LeeGillie/lumos-ultra-exhaust-monitor/cad/out/render_side.png

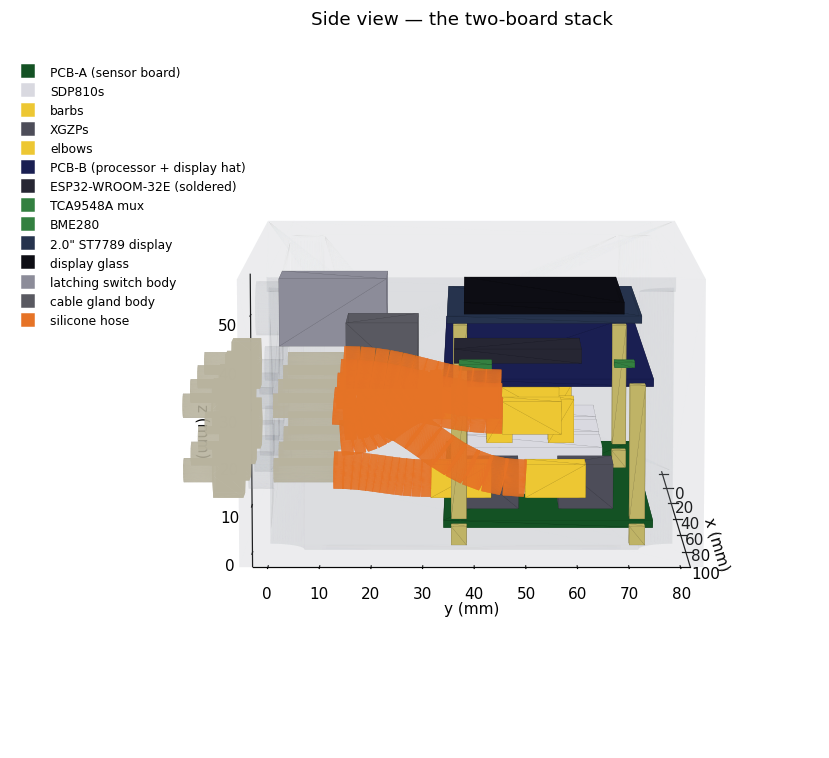
cad/out/render_side.png
