LeeGillie/lumos-ultra-exhaust-monitor/cad/out/render_top.png

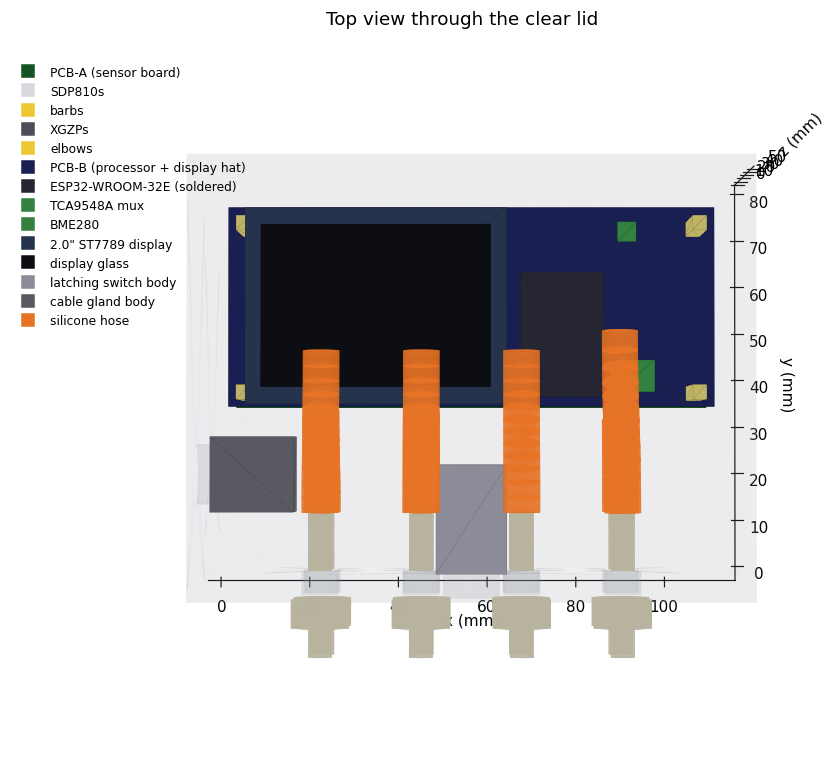
cad/out/render_top.png
