LeeGillie/lumos-ultra-exhaust-monitor/docs/3D Models/Project/renders/sensor_bay_v1.png

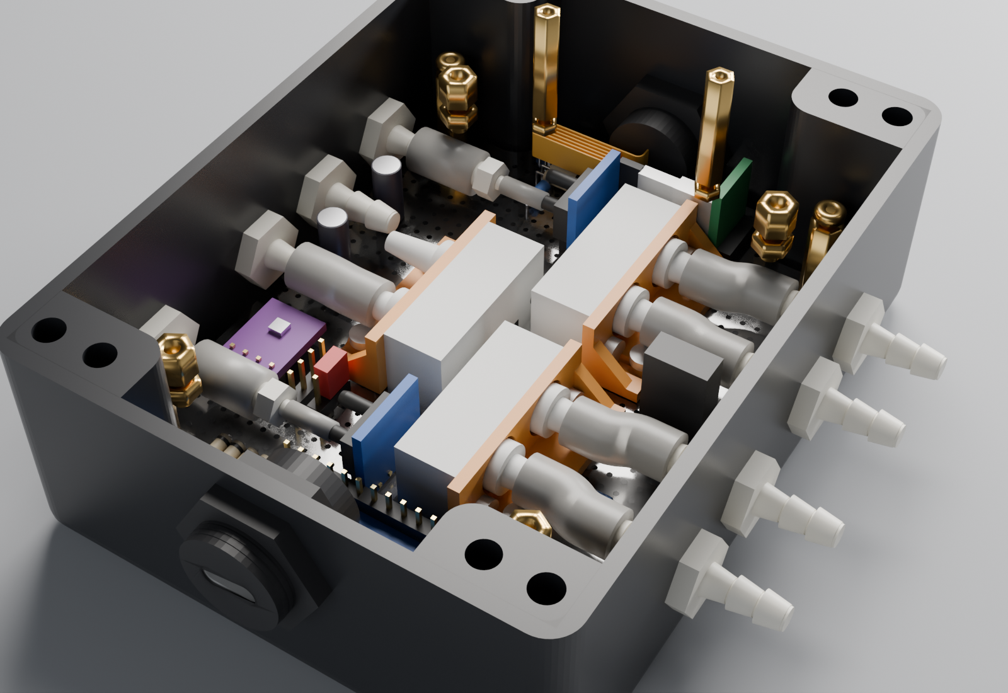
docs/3D Models/Project/renders/sensor_bay_v1.png
