LeeGillie/lumos-ultra-exhaust-monitor/docs/3D Models/Project/textures/mark_fan_node_ANT.png

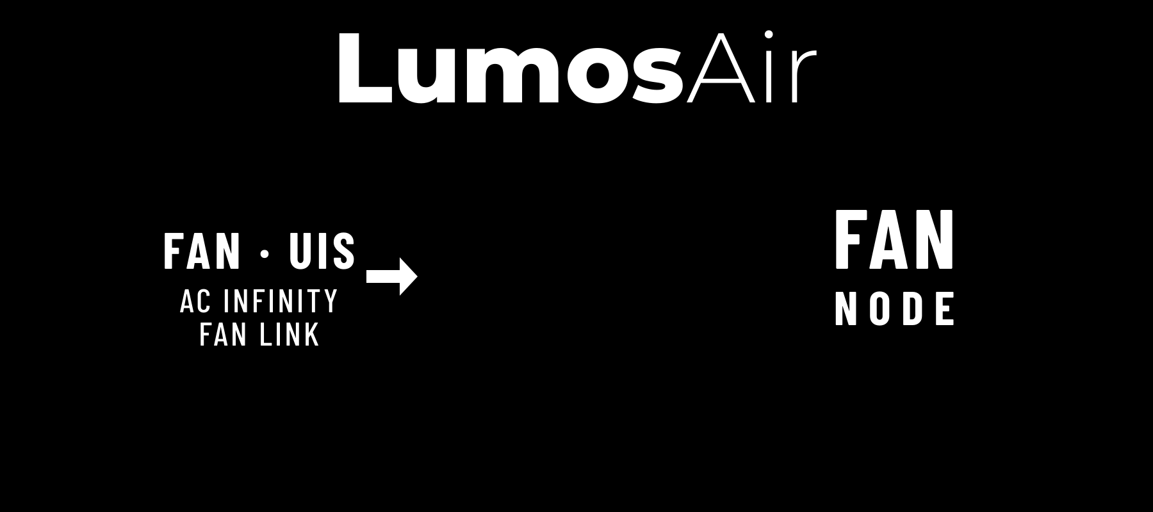
docs/3D Models/Project/textures/mark_fan_node_ANT.png
