LeeGillie/lumos-ultra-exhaust-monitor/docs/3D Models/Project/textures/mark_fan_node_MX.png

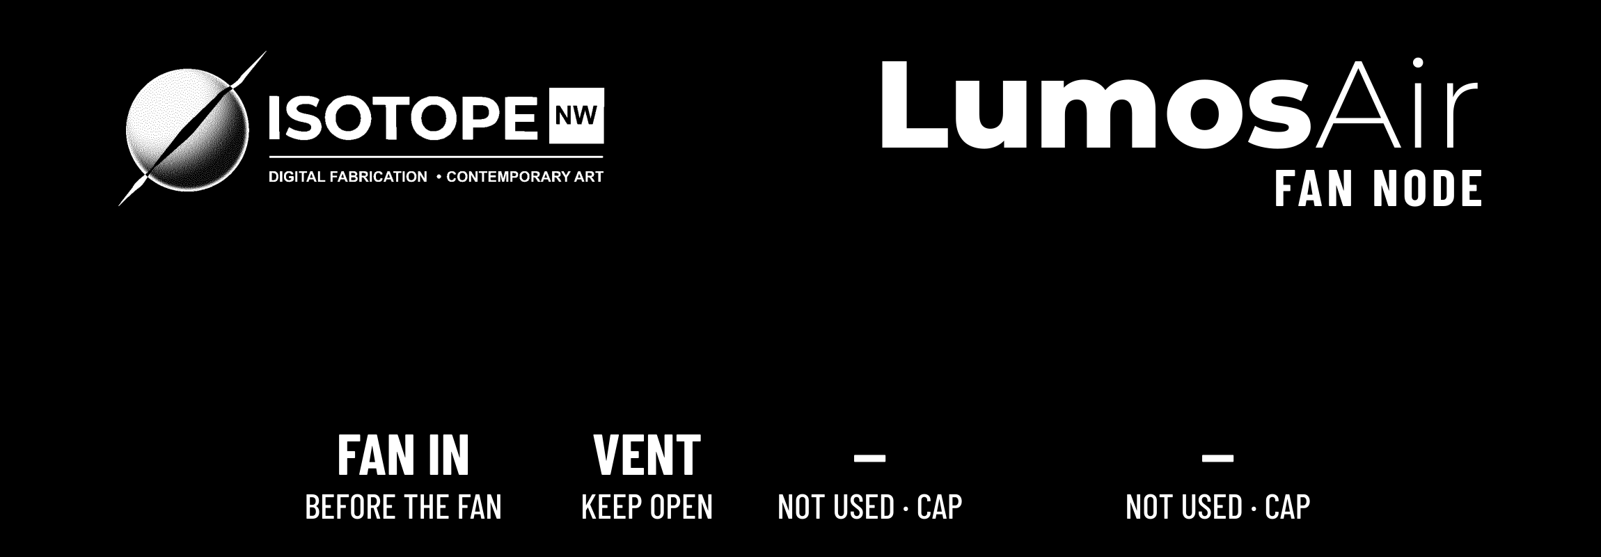
docs/3D Models/Project/textures/mark_fan_node_MX.png
