LeeGillie/lumos-ultra-exhaust-monitor/docs/3D Models/Project/textures/pcb_revB_top_mask.png

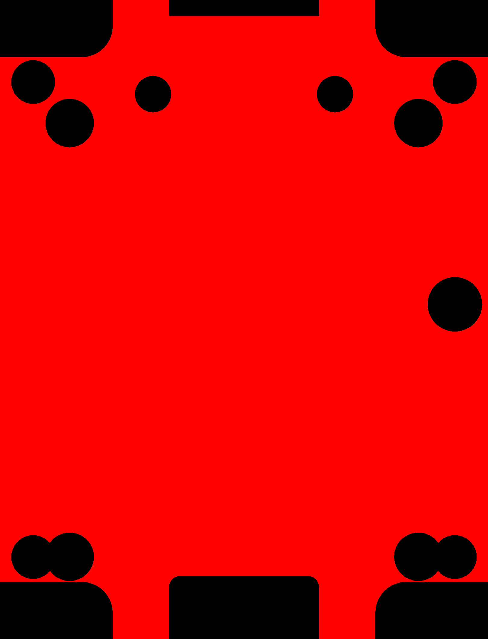
docs/3D Models/Project/textures/pcb_revB_top_mask.png
