LeeGillie/lumos-ultra-exhaust-monitor/docs/datasheets/71mU7P1AoIL._AC_SL1500_.png

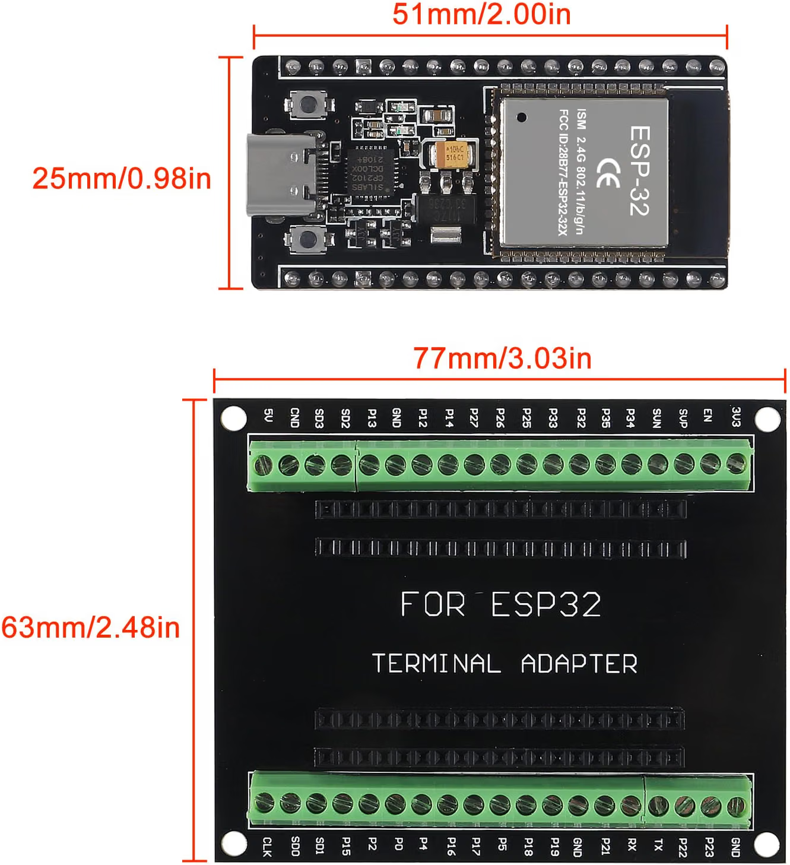
docs/datasheets/71mU7P1AoIL._AC_SL1500_.png
