LeeGillie/lumos-ultra-exhaust-monitor/docs/datasheets/SDP810_dimensions.png

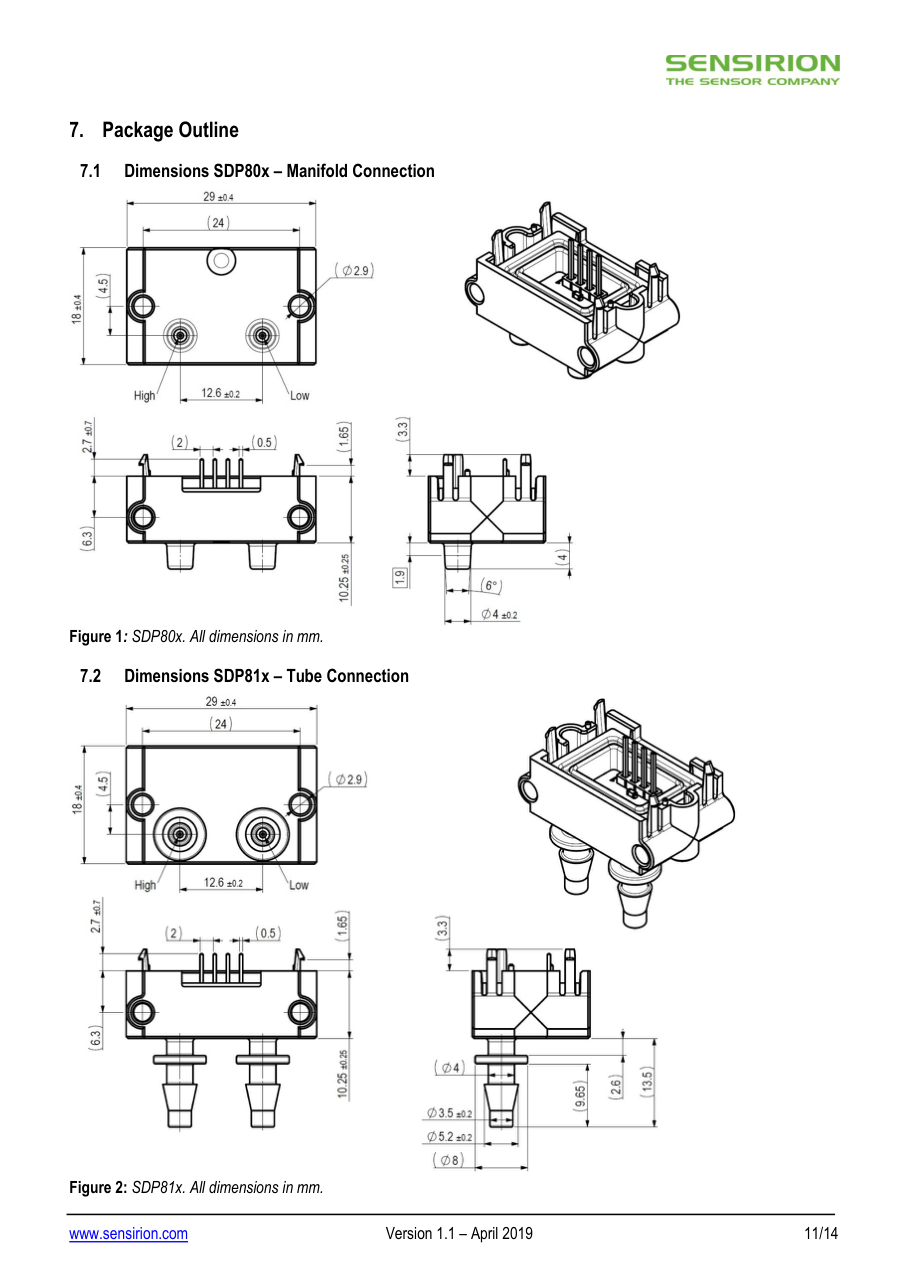
docs/datasheets/SDP810_dimensions.png
